philips-software/amp-postmaster/postmaster/instantiations/HttpServerFrontEnd.hpp

#ifndef POSTMASTER_HTTP_SERVER_FRONT_END_HPP
#define POSTMASTER_HTTP_SERVER_FRONT_END_HPP

#include "generated/page_contents/IndexHtml.hpp"
#include "generated/page_contents/StyleCss.hpp"
#include "generated/page_contents/UploadJs.hpp"
#include "postmaster/application/HttpPageConfiguration.hpp"
#include "postmaster/frontend/AuthenticatedHttpPage.hpp"
#include "postmaster/frontend/ReportingHttpServer.hpp"
#include "services/network/HttpServer.hpp"
#include "services/util/ConfigurationStore.hpp"

namespace main_
{
    struct HttpServerFrontEnd
        : public services::Stoppable
    {
        HttpServerFrontEnd(services::ConnectionFactory& connectionFactory, services::ConfigurationStoreAccess<infra::BoundedString>& hostname,
            services::ConfigurationStoreAccess<infra::BoundedString>& attributes, services::ConfigurationStoreAccess<infra::BoundedString>& password,
            application::Authentication& authentication, const infra::Function<void(bool open, services::IPAddress address)>& reporter, const infra::Function<void(bool receiving)>& receivingTarget, const infra::Function<void(bool receiving)>& receivingSelf);

        void Stop(const infra::Function<void()>& onDone) override
        {
            server.Stop(onDone);
        }

        services::HttpPageWithContent frontendHtml{ "", page_contents::indexHtml, "text/html;charset=UTF-8" };
        services::HttpPageWithContent frontendCss{ "style.css", page_contents::styleCss, "text/css" };
        services::HttpPageWithContent frontendJs{ "upload.js", page_contents::uploadJs, "text/javascript" };
        application::AuthenticatedHttpPage::WithPage<application::HttpPageConfiguration> configuration;

        application::ReportingHttpServer::WithBuffer<8192> server;
    };
}

#endif
