philips-software/amp-postmaster/postmaster/instantiations_st/Display.cpp

#include "postmaster/instantiations_st/Display.hpp"

namespace main_
{
    Display::Display(const postmaster_configuration::Configuration& configuration, services::ConfigurationStoreInterface& configurationStore)
        : viewStatus{ std::chrono::milliseconds(25), 1, std::chrono::seconds(2), configuration.hostname, configurationStore }
        , networkQrCode{ configuration.password }
    {
        displayView.SetViewRegion(display.DisplayRegion());

        layoutViewHorizontal.Add(networkQrCode);
        layoutViewHorizontal.AddFill(layoutView, 1);
        layoutView.AddFill(viewStatus.Scrolling(), 1);
        layoutView.AddFill(viewNetworkStatus.Scrolling(), 1);
        layoutViewHorizontal.ResetLayout();
    }
}
