philips-software/amp-postmaster/postmaster/instantiations_st/EthernetPostmaster.hpp

#ifndef POSTMASTER_ETHERNET_POSTMASTER_HPP
#define POSTMASTER_ETHERNET_POSTMASTER_HPP

#include "hal_st/stm32fxxx/ResetStm.hpp"
#include "hal_st/synchronous_stm32fxxx/SynchronousRandomDataGeneratorStm.hpp"
#include "hal_st_lwip/instantiations_lwip/Ethernet.hpp"
#include "postmaster/application/ViewStatus.hpp"
#include "postmaster/instantiations/Configuration.hpp"
#include "postmaster/instantiations_st/NetworkConnected.hpp"

namespace main_
{
    struct EthernetPostmaster
    {
        EthernetPostmaster(infra::MemoryRange<const std::pair<hal::Port, uint8_t>> ethernetPins, Configuration& configuration, hal::Flash& upgradePack, UartCreator& uartProgrammerCreator, UartCreator& uartExternalCreator, application::ViewStatus& viewStatus)
            : upgradePack(upgradePack)
            , uartProgrammerCreator(uartProgrammerCreator)
            , uartExternalCreator(uartExternalCreator)
            , viewStatus(viewStatus)
            , hostname{ configuration.store, configuration.store.Configuration().hostname }
            , attributes{ configuration.store, configuration.store.Configuration().attributes }
            , password{ configuration.store, configuration.store.Configuration().password }
            , authentication{ password, randomDataGenerator }
            , networkCreator([this](std::optional<main_::NetworkConnected>& value, services::LightweightIp& lightweightIp)
                  {
                      value.emplace(lightweightIp, hostname, attributes, password, authentication, this->upgradePack, this->uartProgrammerCreator, this->uartExternalCreator, this->reset, this->viewStatus);
                  })
            , zeroTerminatedHostname([&configuration]()
                  {
                      infra::BoundedString::WithStorage<65> result{ configuration.store.Configuration().hostname };
                      result.push_back(0);
                      return result;
                  }())

            , ethernet{ ethernetPins, configuration.DeviceMacAddress(), zeroTerminatedHostname, randomDataGenerator, networkCreator }
        {}

        hal::Flash& upgradePack;
        UartCreator& uartProgrammerCreator;
        UartCreator& uartExternalCreator;
        application::ViewStatus& viewStatus;

        hal::ResetStm reset;
        hal::SynchronousRandomDataGeneratorStm randomDataGenerator;

        services::ConfigurationStoreAccess<infra::BoundedString> hostname;
        services::ConfigurationStoreAccess<infra::BoundedString> attributes;
        services::ConfigurationStoreAccess<infra::BoundedString> password;
        application::Authentication authentication;
        infra::Creator<services::Stoppable, main_::NetworkConnected, void(services::LightweightIp& lightweightIp)> networkCreator;

        infra::BoundedString::WithStorage<65> zeroTerminatedHostname = {};
        main_::Ethernet<3, 0, 4> ethernet;
    };
}

#endif
