philips-software/amp-postmaster/postmaster/instantiations_st/NetworkConnected.hpp

#ifndef POSTMASTER_NETWORK_CONNECTED_HPP
#define POSTMASTER_NETWORK_CONNECTED_HPP

#include "generated/Version.h"
#include "lwip/lwip_cpp/LightweightIp.hpp"
#include "postmaster/application/MdnsDiscovery.hpp"
#include "postmaster/application/ViewNetworkStatus.hpp"
#include "postmaster/application/ViewStatus.hpp"
#include "postmaster/instantiations/EchoServer.hpp"
#include "postmaster/instantiations/Mdns.hpp"
#include "postmaster/instantiations_st/HttpServerSt.hpp"

namespace main_
{
    struct NetworkConnected
        : public services::Stoppable
    {
        NetworkConnected(services::LightweightIp& lightweightIp, services::ConfigurationStoreAccess<infra::BoundedString>& hostname,
            services::ConfigurationStoreAccess<infra::BoundedString>& attributes, services::ConfigurationStoreAccess<infra::BoundedString>& password,
            application::Authentication& authentication,
            hal::Flash& upgradePack, UartCreator& uartProgrammerCreator, UartCreator& uartExternalCreator, hal::Reset& reset, application::ViewStatus& viewStatus)
            : mdns{ *hostname, lightweightIp, lightweightIp, lightweightIp.GetIPv4Address(), Postmaster::generated::VERSION, Postmaster::generated::VERSION_FULL, *attributes }
            , mdnsDiscovery{ lightweightIp, lightweightIp }
            , httpServer{ lightweightIp, hostname, attributes, password, authentication, mdnsDiscovery.discovery, uartProgrammerCreator, uartExternalCreator, upgradePack, reset, [&viewStatus](bool open, services::IPAddress address)
                {
                    viewStatus.SetConnectionOpen(open, address);
                },
                [&viewStatus](bool receiving)
                {
                    viewStatus.SetReceivingTarget(receiving);
                },
                [&viewStatus](bool receiving)
                {
                    viewStatus.SetReceivingSelf(receiving);
                } }
            , echoServer{ lightweightIp, uartExternalCreator, 1235 }
            , traceForwarder(lightweightIp)
        {}

        void Stop(const infra::Function<void()>& onDone) override
        {
            httpServer.Stop(onDone);
        }

        main_::Mdns mdns;
        main_::MdnsDiscovery mdnsDiscovery;
        main_::HttpServerSt httpServer;
        main_::EchoServer echoServer;
        main_::SingleConnectionLink link{ httpServer.server, echoServer.listener };
        main_::TraceForwarderSt traceForwarder;
    };
}

#endif
